7-liang/tp32/img/04.jpg

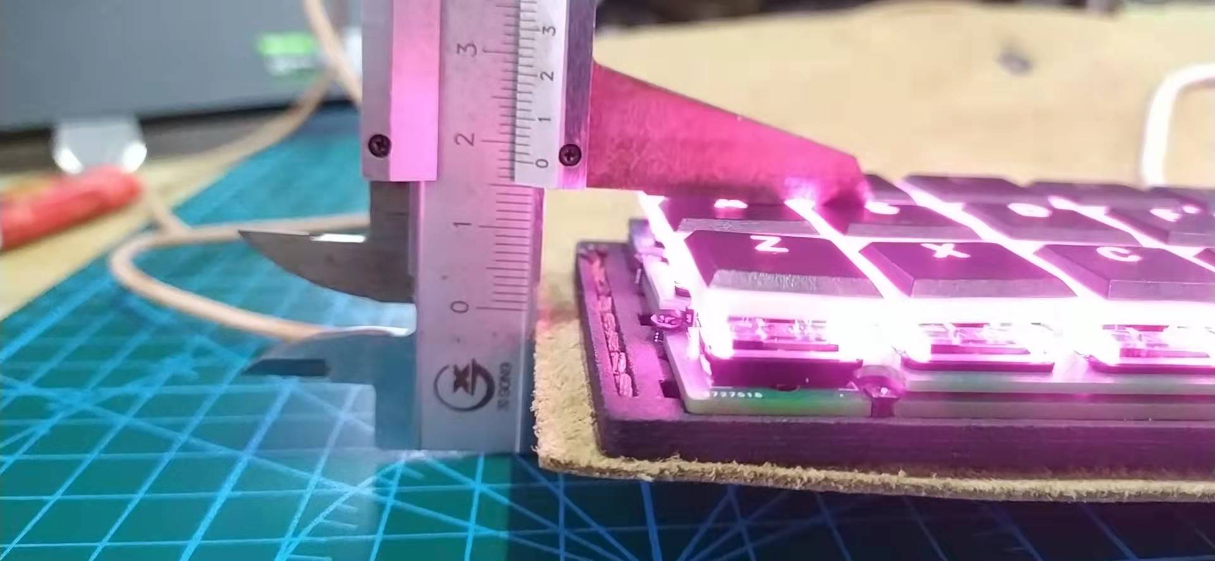
img/04.jpg
