7-liang/tp32/img/06.jpg

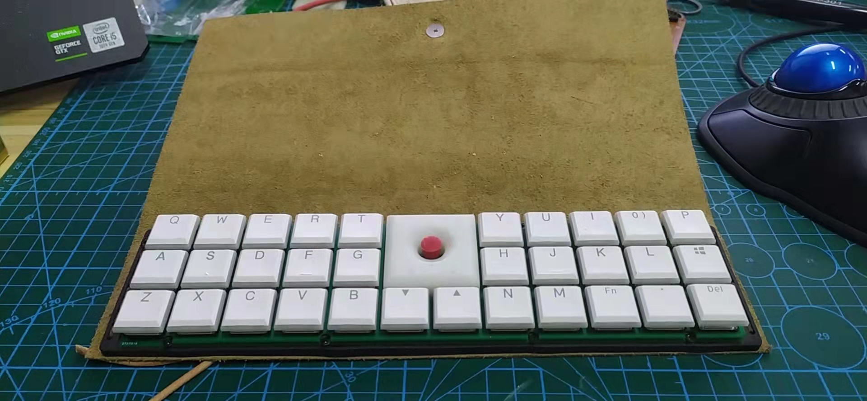
img/06.jpg
