7-liang/tp32/img/07.jpg

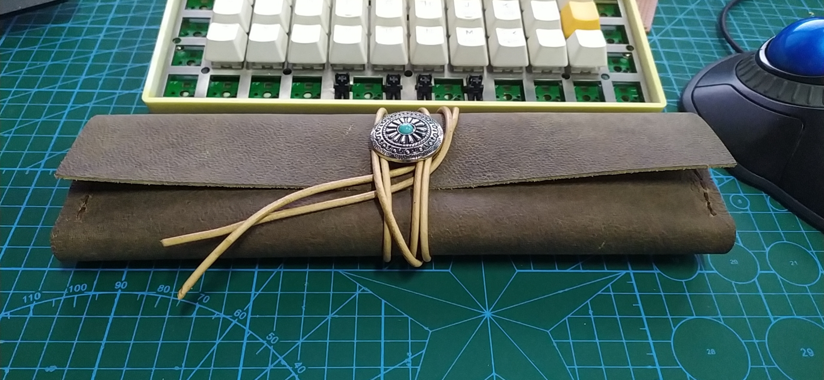
img/07.jpg
