7-liang/tp32/img/08.jpg

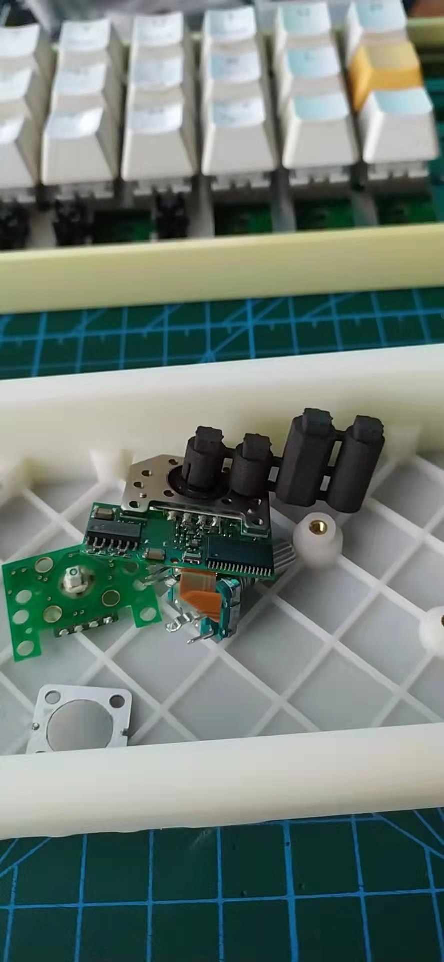
img/08.jpg
